x653/xv6-riscv-fpga/xv6-riscv/kernel/sysproc.c

#include "types.h"
#include "riscv.h"
#include "defs.h"
#include "param.h"
#include "memlayout.h"
#include "spinlock.h"
#include "proc.h"

uint32
sys_exit(void)
{
  int n;
  argint(0, &n);
  exit(n);
  return 0;  // not reached
}

uint32
sys_getpid(void)
{
  return myproc()->pid;
}

uint32
sys_fork(void)
{
  return fork();
}

uint32
sys_wait(void)
{
  uint32 p;
  argaddr(0, &p);
  return wait(p);
}

uint32
sys_sbrk(void)
{
  uint32 addr;
  int n;

  argint(0, &n);
  addr = myproc()->sz;
  if(growproc(n) < 0)
    return -1;
  return addr;
}

uint32
sys_sleep(void)
{
  int n;
  uint ticks0;

  argint(0, &n);
  acquire(&tickslock);
  ticks0 = ticks;
  while(ticks - ticks0 < n){
    if(killed(myproc())){
      release(&tickslock);
      return -1;
    }
    sleep(&ticks, &tickslock);
  }
  release(&tickslock);
  return 0;
}

uint32
sys_kill(void)
{
  int pid;

  argint(0, &pid);
  return kill(pid);
}

// return how many clock tick interrupts have occurred
// since start.
uint32
sys_uptime(void)
{
  uint xticks;

  acquire(&tickslock);
  xticks = ticks;
  release(&tickslock);
  return xticks;
}

// return number of free memory pages
uint32
sys_memory(void)
{
  return kmemory();
}
