x653/xv6-riscv-fpga/fpga/boot/types.h

typedef unsigned int   uint;
typedef unsigned short ushort;
typedef unsigned char  uchar;

typedef unsigned char uint8;
typedef unsigned short uint16;
typedef unsigned int  uint32;
typedef unsigned long long uint64;
